aderusha/HASwitchPlate/Documentation/Images/Arduino_Erase_All_Flash_Contents.png

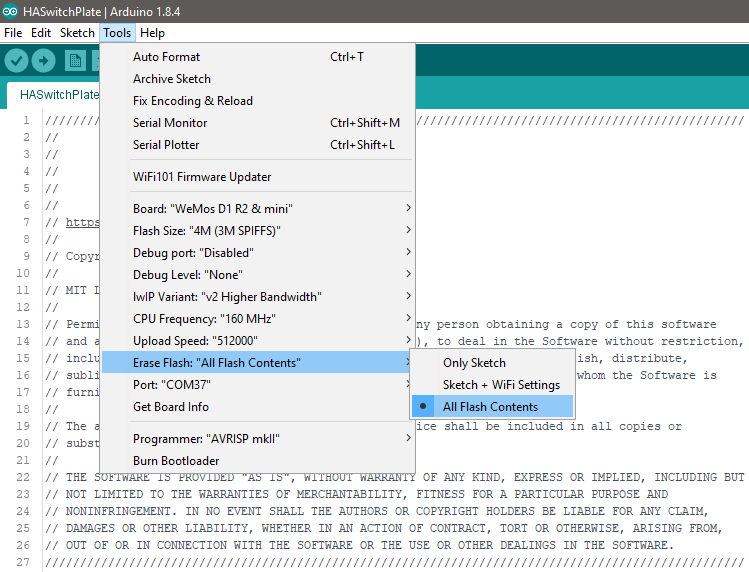
Documentation/Images/Arduino_Erase_All_Flash_Contents.png
