aderusha/HASwitchPlate/Documentation/Images/hasp_Core_Functionality.png

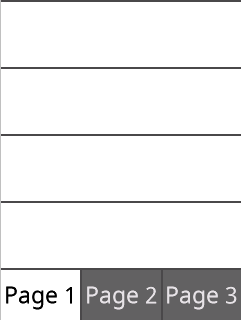
Documentation/Images/hasp_Core_Functionality.png
