aderusha/HASwitchPlate/Documentation/Images/hasp_Display_Media_Control_page8.png

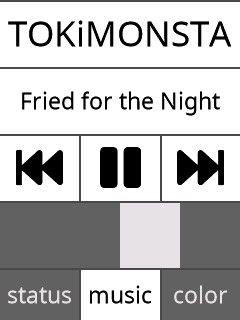
Documentation/Images/hasp_Display_Media_Control_page8.png
