aderusha/HASwitchPlate/Documentation/Images/hasp_Theme_Dark_on_Light.png

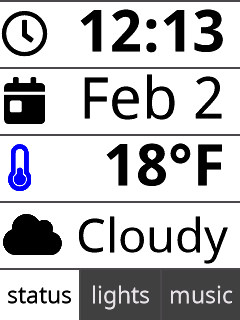
Documentation/Images/hasp_Theme_Dark_on_Light.png
