aderusha/HASwitchPlate/Documentation/Images/hasp_Theme_Light_on_Dark.png

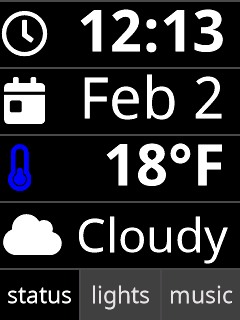
Documentation/Images/hasp_Theme_Light_on_Dark.png
