aderusha/HASwitchPlate/Documentation/Images/HASwitchPlate_Demo_3x3.png

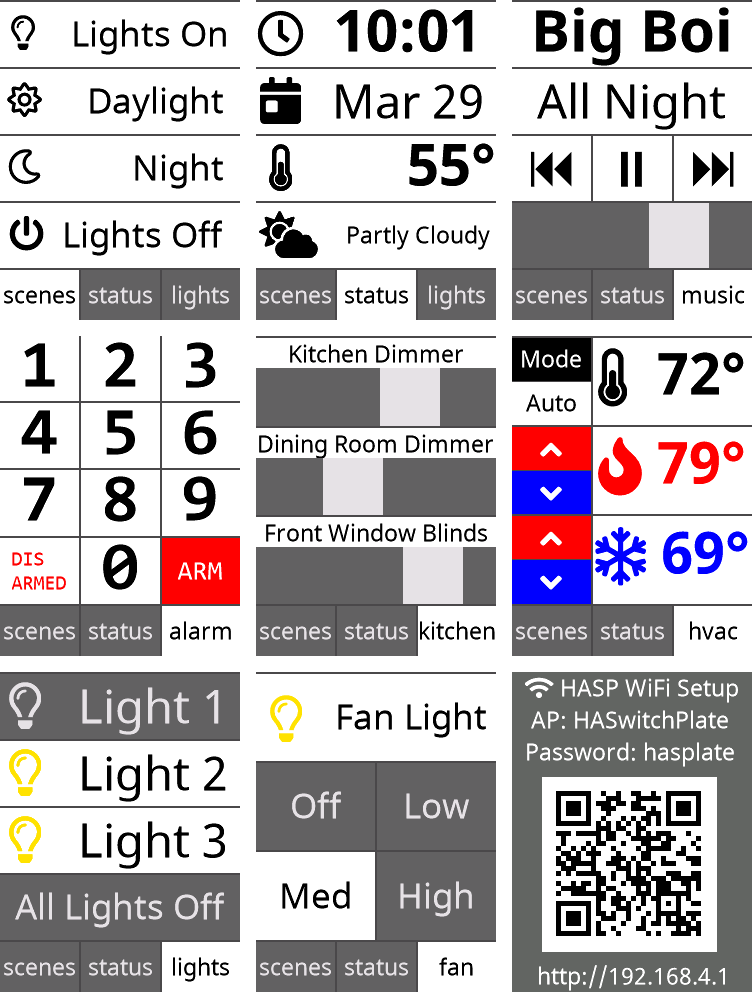
Documentation/Images/HASwitchPlate_Demo_3x3.png
