aderusha/HASwitchPlate/Documentation/Images/HASwitchPlate_Techpen-Isometric.png

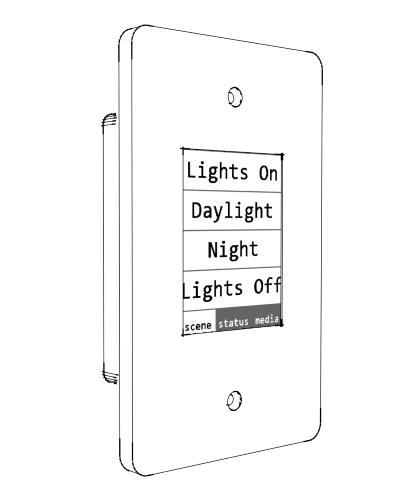
Documentation/Images/HASwitchPlate_Techpen-Isometric.png
