aderusha/HASwitchPlate/Documentation/Images/HASwitchPlate_Three_Model_Variations_800px.png

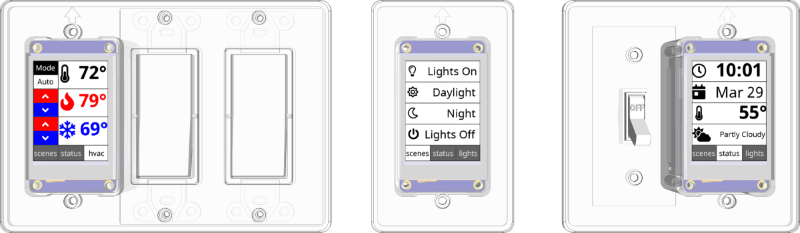
Documentation/Images/HASwitchPlate_Three_Model_Variations_800px.png
