aderusha/HASwitchPlate/Documentation/Images/NextionUI_p9_2buttons+graph.png

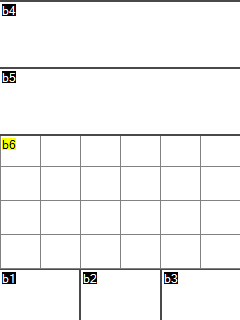
Documentation/Images/NextionUI_p9_2buttons+graph.png
