aderusha/HASwitchPlate/3D_Printable_Models/HASwitchPlate_desktop_front.stl

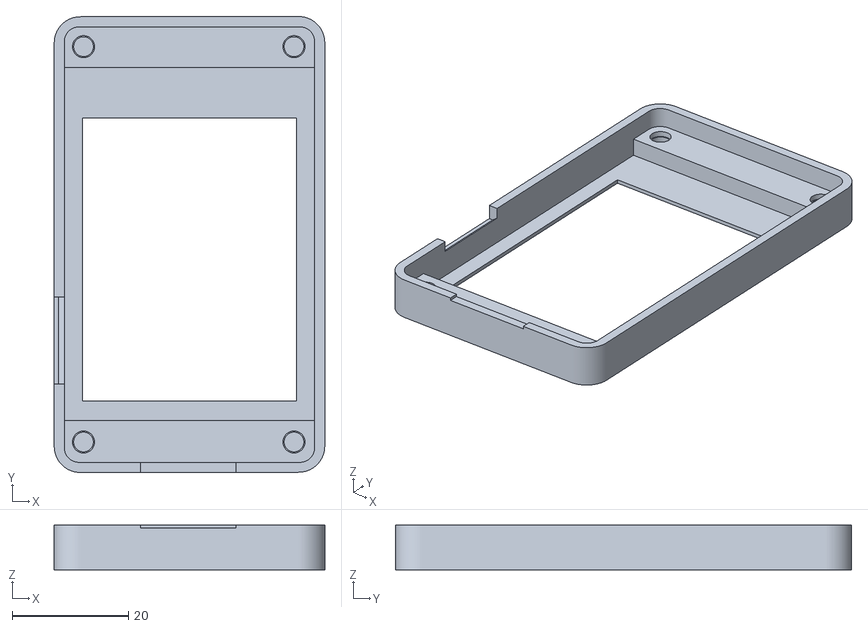
[picture p57: CAD file, 2019-02-07]
3D_Printable_Models/HASwitchPlate_desktop_front.stl
46.6 x 78.5 x 7.70
