aderusha/HASwitchPlate/3D_Printable_Models/HASwitchPlate_desktop_base.stl

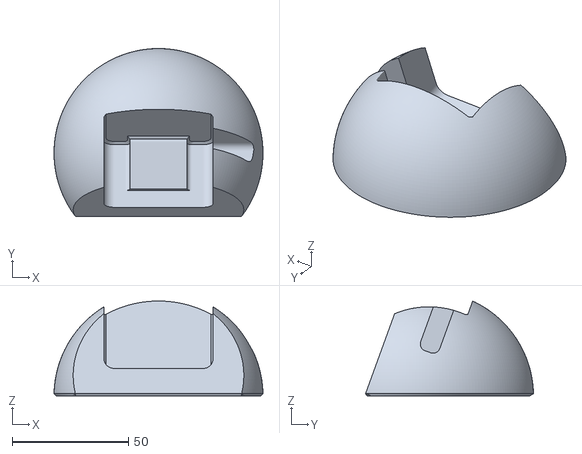
[picture p59: CAD file, 2018-12-18]
3D_Printable_Models/HASwitchPlate_desktop_base.stl
90.0 x 72.3 x 40.9
