aderusha/HASwitchPlate/3D_Printable_Models/HASwitchPlate_rear_dev.stl

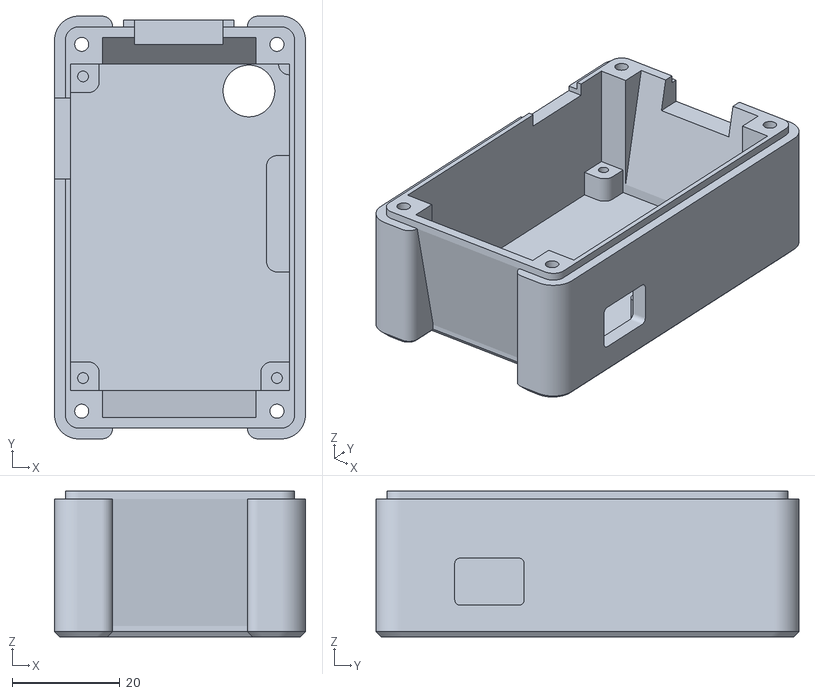
[picture p60: CAD file, 2018-12-04]
3D_Printable_Models/HASwitchPlate_rear_dev.stl
46.6 x 78.5 x 27.1
