aderusha/HASwitchPlate/3D_Printable_Models/HASwitchPlate_front_single_UK-UNTESTED.stl

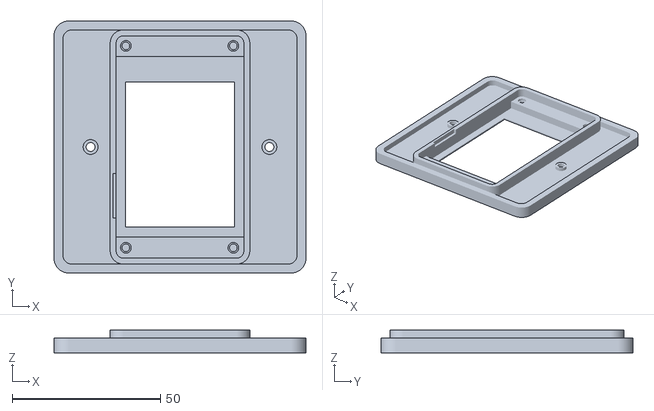
[picture p61: CAD file, 2018-06-04]
3D_Printable_Models/HASwitchPlate_front_single_UK-UNTESTED.stl
85.0 x 85.0 x 7.70
