aderusha/HASwitchPlate/Documentation/Images/HASP_3D_Print_Models.png

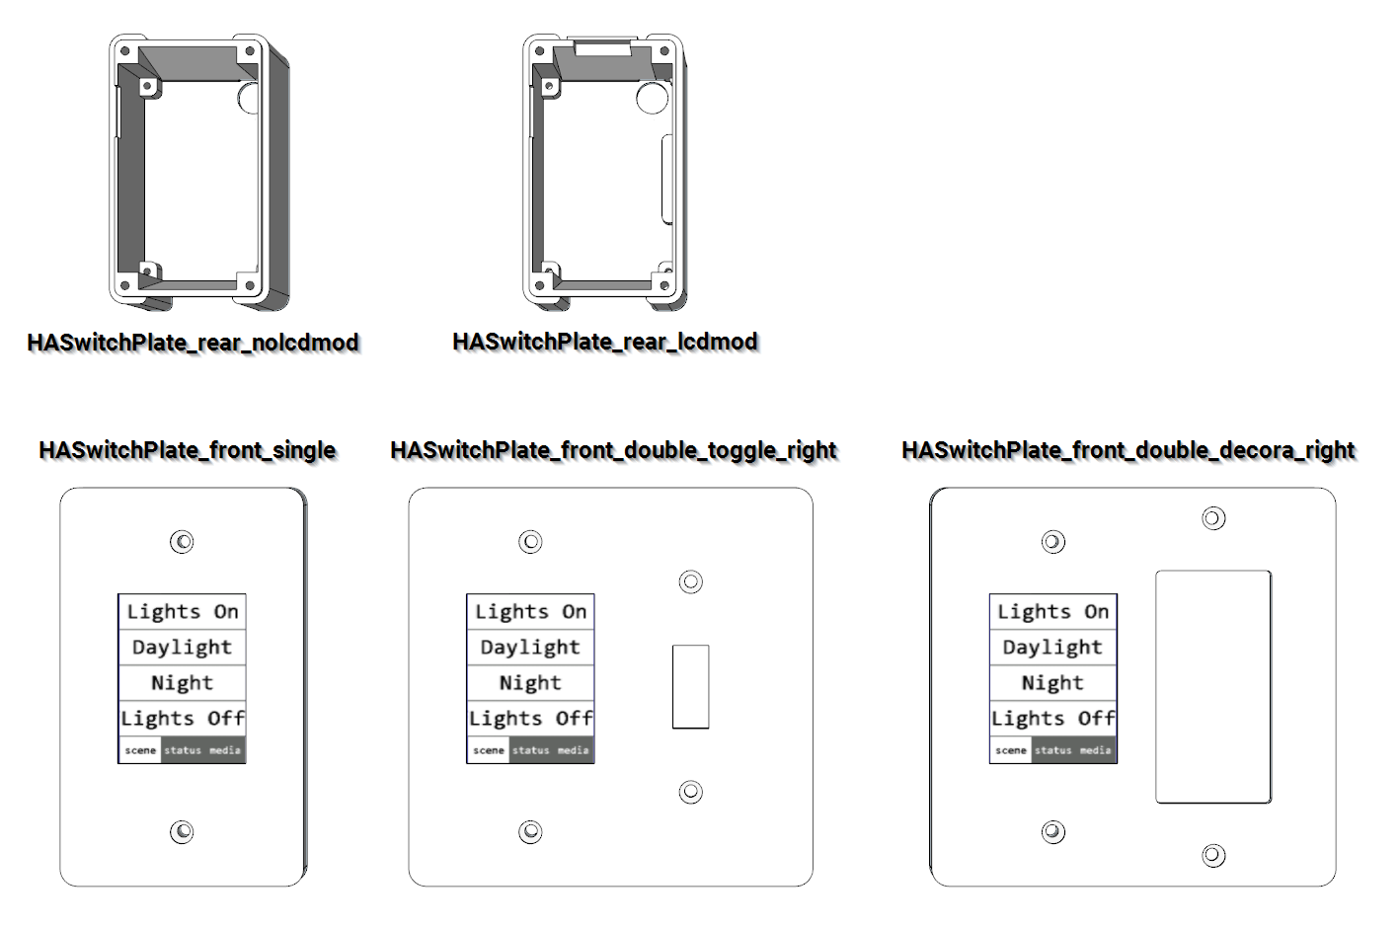
Documentation/Images/HASP_3D_Print_Models.png
